fablabwinti/RFID_Machine_Controller/Firmware/Fablab_RFID_control/display.h

#include <Fonts/FreeSansBold12pt7b.h>


// "Fonts/g9regular.h" already included in global.h
#include "Fonts/g12bold.h"



#if (SSD1306_LCDHEIGHT != 64)
#error("Display height not set to 64 pixels, please fix Adafruit_SSD1306.h!");
#endif

#define POSTLOGOUTDISPLAYTIME 10 //time in seconds user info is displayed after logout


//logo generated using http://javl.github.io/image2cpp/
//note on icon generation: the library can only display bitmaps with the x dimension being a multiple of 8 so all icons must be in this format, other dimension screw up the displayed image
//the default settings on the webpage are fine (horizontal mode)

unsigned char fablablogo []  = {
  0x00, 0x00, 0x00, 0x00, 0x00, 0x00, 0x00, 0x00, 0x00, 0x00, 0x00, 0x7f, 0xf8, 0x00, 0x00, 0x00,
  0x00, 0x00, 0x07, 0xff, 0xff, 0x80, 0x00, 0x00, 0x00, 0x00, 0x1f, 0xff, 0xff, 0xf0, 0x00, 0x00,
  0x00, 0x00, 0x7f, 0x80, 0x07, 0xfc, 0x00, 0x00, 0x00, 0x01, 0xf8, 0x00, 0x00, 0x3f, 0x00, 0x00,
  0x00, 0x07, 0xe0, 0x00, 0x00, 0x1f, 0x80, 0x00, 0x00, 0x0f, 0x80, 0x00, 0x00, 0x07, 0xc0, 0x00,
  0x00, 0x1e, 0x00, 0x7f, 0xf8, 0x03, 0xe0, 0x00, 0x00, 0x3c, 0x03, 0xff, 0xff, 0x00, 0xf0, 0x00,
  0x00, 0x78, 0x0f, 0xfc, 0xff, 0xc0, 0x78, 0x00, 0x00, 0xf0, 0x3f, 0xf0, 0x7f, 0xf0, 0x3c, 0x00,
  0x01, 0xe0, 0xff, 0xe0, 0x1f, 0xf8, 0x1e, 0x00, 0x03, 0xc1, 0xff, 0x80, 0x07, 0xfe, 0x0f, 0x00,
  0x07, 0x83, 0xff, 0xe0, 0x01, 0xff, 0x07, 0x00, 0x07, 0x07, 0xff, 0xff, 0xe0, 0xff, 0x87, 0x80,
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
  0x3E, 0x00, 0x00, 0x7C, 0x1C, 0x00, 0x00, 0x38
};

//print the header: machine name and status icons
void displayAddHeader(void) {

  display.setFont(&g9regularFont);
  display.setCursor(0, 7);


  display.print(config.MachineName);

  if (WiFi.status() == WL_CONNECTED)
  {

    display.drawBitmap(94, 0, wifiokicon, 9, 7, 1);
  }
  else
  {
    display.drawBitmap(94, 0, wififailicon, 9, 7, 1);
  }
  if (userDBupdated)
  {
    display.drawBitmap(105, 0, DBokicon, 6, 7, 1);
  }
  else
  {
    display.drawBitmap(105, 0, DBfailicon, 6, 7, 1);
  }
  if (serverhealthy)
  {
    display.drawBitmap(113, 0, serverokicon, 7, 7, 1);
  }
  else
  {
    display.drawBitmap(113, 0, serverfailicon, 7, 7, 1);

  }

  if (SDcardOK)
  {
    display.drawBitmap(122, 0, SDokicon, 8, 7, 1);
  }
  else
  {
    display.drawBitmap(122, 0, SDfailicon, 8, 7, 1);
  }

  display.drawFastHLine(0, 8, 128, 1); //draw horizontal line
}

//display user info during login or post logout
void displayUserInfo(void)
{
  String fullname;
  //String firstname;
  //String surname;
  if (currentuser == 0) //the admin tag is logged in
  {
    fullname = "MASTER KEY";
  }
  else
  {
    //get current users name from database
    userdatabase.readRec(currentuser, EDB_REC userentry); //get the currently logged in user entry
    fullname = String(userentry.name);
    //firstname = splitStringbySeparator(fullname, char(' ')); //split the name string into first name and surname
    //surname = fullname.substring(firstname.length() + 1);
  }

  if (machineLocked)
  {
    fullname = " "; //currentuser is 0 after logout, so name is no longer available (TODO: could save the 'lastuser' number in a global variable or something)
  }

  display.setFont(&g12boldFont);
  display.setCursor(0, 21);
  display.print(fullname);//String(userentry.name));

  //display.print(0, 27);
  //display.print(surname);
  display.setFont(&FreeSansBold12pt7b);

  time_t timeinuse;
  if (machineLocked) //if no user is logged in, this is a post logout call, display static time of time used
  {
    timeinuse = userStoptime - userStarttime;
  }
  else
    timeinuse = getRtcTimestamp() - userStarttime;

  uint16_t usehours = timeinuse / 3600;
  uint16_t useminutes = (timeinuse % 3600) / 60;
  uint16_t useseconds = timeinuse % 60;

  char temparr[12];
  // getTextBounds considers the bitmap size, not the advance width, so the
  // text width differs for a narrow glyph like '1' at the end, which makes
  // the text jump around. To avoid that, append a dummy char of known width
  // for measuring and remove it for rendering.
  snprintf(temparr, sizeof(temparr), "%u:%02u:%02u.", usehours, useminutes, useseconds);
  int16_t x, y;
  uint16_t w1, w2, h;
  display.getTextBounds(temparr, 0, 0, &x, &y, &w1, &h);
  temparr[strlen(temparr) - 1] = '\0';
  w1 -= 5;
  display.setCursor(64 - w1 / 2, 46);
  display.print(temparr);


  //running cost is calculated from:
  // config.mPrice //price per period in cents
  // config.mPeriod //pricing period in minutes
  //config.mMinPeriods /minimum periods that are billed
  //to not bill accidental login, the first 30 seconds are free

  uint16_t cost = 0; //cost in cents
  if(timeinuse > 30) //after 30 seconds, start counting cost, bill the minimum amount, then increase by pricing period
  {
    //initially, bill the minimum number of periods
    cost = config.mMinPPrice;
    //after minimum number of periods, start counting periods
    if(timeinuse > 60*(time_t)config.mMinPeriods*(time_t)config.mPeriod) 
    {
      time_t periodSeconds = 60*(time_t)config.mPeriod;
      uint16_t numberofperiods = (timeinuse + periodSeconds - 1)/periodSeconds; // rounded up
      cost += (numberofperiods - config.mMinPeriods)*config.mPrice;
    }
  }
  
  snprintf(temparr, sizeof(temparr), "%d.%02d.", cost / 100, cost % 100);
  display.setFont(&g12boldFont);
  display.getTextBounds(temparr, 0, 0, &x, &y, &w1, &h);
  temparr[strlen(temparr) - 1] = '\0';
  w1 -= 3;
  display.setCursor(128 - w1, 63);
  display.print(temparr);
  display.setFont(&g9regularFont);
  display.getTextBounds("CHF", 0, 0, &x, &y, &w2, &h);
  display.setCursor(128 - w1 - w2 - 5, 63);
  display.print("CHF");

}

void displayUpdate(void) {


  //stuff to display: time
  //currently logged in user

  //if machine is unused:
  //display the current time, maybe also the date, what else?
  display.clearDisplay();
  displayAddHeader();


  if (machineLocked) //machine not in use
  {
    if ( postlogoutmillis > 0 && millis() < postlogoutmillis + (long)POSTLOGOUTDISPLAYTIME * 1000) //user just logged out, postlogoutmillis is set to 0 after postlogout switchoff (of after 30 seconds, whichever one is longer)
    {
      displayUserInfo();
    }
    else //idle
    {
      char temparr[11];
      snprintf(temparr, sizeof(temparr), "%02u.%02u.%04u", day(), month(), year());
      display.setFont(&g9regularFont);
      display.setCursor(37, 33);
      display.print(temparr);
      snprintf(temparr, sizeof(temparr), "%02u:%02u:%02u", hour(), minute(), second());
      display.setFont(&g12boldFont);
      display.setCursor(35, 47);
      display.print(temparr);

      //todo: remove this debug IP output (or if it is deemed useful in production, properly integrate it into the layout)

      if (WiFi.status() == WL_CONNECTED)
      {
        display.setFont(&g9regularFont);
        display.setCursor(0, 63);
        display.print(F("IP: "));
        display.print(WiFi.localIP());
      }
    }
  }
  else //machine is unlocked, user is logged in
  {
    displayUserInfo();
  }

  display.display();

  // char numberbuffer[6];
  //dtostrf(1234, 6, 2, numberbuffer);
  //display.print(numberbuffer);

}


void displayLogin(void)
{
  display.clearDisplay();
  displayAddHeader();

  //todo: display username of recognized tag
#if 0
  display.setFont(&g12boldFont);
  display.setCursor(0, 21);
  display.print("Master");
#endif
  display.setFont(&FreeSansBold12pt7b);
  display.setCursor(44, 51);

  // display.drawBitmap(3, 30, accepticon, 24, 24, 1);
  //display.setFont(&Dialogbold20);
  // display.setCursor(38, 48);

  display.print("Start   ");
  display.drawXBitmap(5, 27, check_xbm_bits, check_xbm_width, check_xbm_height, 1);
  display.display();
}

void displayLogout(void)
{
  display.clearDisplay();
  displayAddHeader();

  //todo: display username of recognized tag
#if 0
  display.setFont(&g12boldFont);
  display.setCursor(0, 21);
  display.print("name");
#endif
  display.setFont(&FreeSansBold12pt7b);
  display.setCursor(44, 51);

  // display.drawBitmap(3, 30, accepticon, 24, 24, 1);
  // display.setFont(&Dialogbold20);
  // display.setCursor(38, 48);

  display.print("Stop     ");
  display.drawXBitmap(5, 27, check_xbm_bits, check_xbm_width, check_xbm_height, 1);
  display.display();
}

//display access denied (with a reason)
//reasons: 0 = unauthorized, 1 = occupied, 2 = invalid tag
void displayDenied(uint8_t reason)
{
  display.clearDisplay();
  displayAddHeader();

  display.setFont(&g12boldFont);
  //todo: display username of recognized tag (if any)
#if 0
  display.setFont(&g12boldFont);
  display.setCursor(0, 21);
  display.print("name");
#endif
  display.setCursor(44, 46);

  // display.drawBitmap(0, 30, deniedicon, 24, 24, 1);
  // display.setFont(&Dialogbold12);
  // display.setCursor(25, 46);

  if (reason == 1)
  {
    display.print("besetzt");
  }
  else if (reason == 2)
  {
    display.print("tag error");
  }
  else
  {
    display.print("unberechtigt");
  }
  display.drawXBitmap(5, 27, cross_xbm_bits, cross_xbm_width, cross_xbm_height, 1);
  display.display();
}


void showCloudDownload(void)
{
  display.clearDisplay();
  display.drawBitmap(46, 20, DBdl, 32, 32, 1);
  display.setFont(&g12boldFont);
  display.setCursor(12, 12);
  display.println(F("Updating Database"));
  display.display();
}

void displayinit(void)
{
  display.begin(SSD1306_SWITCHCAPVCC, 0x3C);
  Wire.setClock(400000);  // use fast speed
  display.clearDisplay();
  display.display();  //
  display.setTextSize(1);
  display.setTextColor(WHITE);
  display.setTextWrap(false);

  /*
    display.setCursor(29, 15);
    display.setFont(&FreeSansBold12pt7b);
    display.println("Fablab");
    display.setCursor(30, 54);
    display.print("Winti");
    display.display();
  */
  //delay(500);
  display.drawBitmap(31, 0, fablablogo, 64, 64, 1);
  display.display();
  delay(800);
  display.clearDisplay();
  display.display();

  display.setFont(&g9regularFont);
  display.setCursor(0, 7);


}
