fablabwinti/RFID_Machine_Controller/Firmware/Fablab_RFID_control/WiFi.h

//#include <DNSServer.h>

#define APTIMEOUT (10*60000) //stop accesspoint mode after this time
#define DNS_PORT 53

ESP8266WiFiMulti wifiMulti;
uint8_t wifiConnected;
uint8_t wifiConnectFailCounter;
unsigned long wifiwatchdog = 0; //time keeper for wifi connection
unsigned long APtimestamp = 0; //time keeper for wifi connection
//DNSServer dnsServer;

/*
  void setupMDNS()
  {
  // Call MDNS.begin(<domain>) to set up mDNS to point to
  // "<domain>.local" or in this case alphanode.local
  if (!MDNS.begin("rfidcontrol"))
  {
    Serial.println(F("Error setting up MDNS responder!"));
  }
  else  Serial.println(F("mDNS responder started"));
  }
*/


//host a wifi access point
void wifiHostAP()
{
  //IPAddress apIP(192, 168, 4, 1);
  WiFi.disconnect(true);
  delay(100);
#ifdef SERIALDEBUG
  Serial.print(F("Starting access point. "));
#endif
  WiFi.mode(WIFI_AP); //accesspoint is very unstable if STA mode is on and no wifi connection is available
  WiFi.softAP(config.DeviceName.c_str(), config.DevicePW.c_str());
  //dnsServer.setErrorReplyCode(DNSReplyCode::NoError);
  //dnsServer.start(DNS_PORT, "*", apIP);

  APactive = 2; //AP is up and running
  APtimestamp = millis();
  LEDColor.h = 200; //set LED purple if accesspoint is active
  LEDColor.v = LED_MAXBRIGHTNESS; //high brightness

}

//add accesspoints saved in config to wifiMulti
void wifiConnect(void)
{
  wifiConnected = 0; //if this function is called, we are not yet or no more connected
  uint8_t i;
#ifdef SERIALDEBUG
  Serial.println(F("Connecting to WIFI"));
#endif
  //add all known connections in config to wifi multi:
  for (i = 0; i < MULTIWIFIS ; i++)
  {
    wifiMulti.addAP(config.ssid[i].c_str(), config.wifipass[i].c_str());
#ifdef SERIALDEBUG
    Serial.print(F("Adding Network: "));
    Serial.println(config.ssid[i]);
#endif
  }

  wifiMulti.run(); //connect to wifi (starts the network scan on first call, tries to connect on further calls (in checkconnection function)
}


void wifiAddAP(String name, String password)
{
  uint8_t success = 1;
  uint8_t i;
#ifdef SERIALDEBUG
  Serial.println(name + " " + password);
#endif
  for (i = 0; i < MULTIWIFIS ; i++)
  {
    if (config.ssid[i] == name) //already known,maybe an updated password?
    {

      if (config.wifipass[i] != password) //updated password
      {
        config.wifipass[i] = password;
      }
      else
      {
        success = 0;
      }
    }
  }

  if (success)
  {
    config.ssid[config.nextmultiwifitowrite] = name;
    config.wifipass[config.nextmultiwifitowrite] = password;
    config.nextmultiwifitowrite = (config.nextmultiwifitowrite + 1) % MULTIWIFIS;
    WriteConfig();
#ifdef SERIALDEBUG
    Serial.println(F("wifi saved"));
#endif
  }
}


void wifiCheckConnection()
{

  //todo: set a timeout for connecting to wifi, if connection fails repeatedly, start the AP

  if (APactive > 0)
  {
    if (((millis() - APtimestamp) > APTIMEOUT) )
    {
      WiFi.mode(WIFI_STA); //deactivate access point
      APactive = 0;
      LEDColor.h = 30; //change led color to yellow
      LEDColor.v = LED_DEFAULTBRIGTHNESS;
      ESP.restart(); //todo: this was added because the mdns service does not work after returning from AP mode, can this be fixed some other way?
    }

    if (APactive == 1) wifiHostAP(); //AP was requested, so run it
    else if (APactive == 2)
    {
      LEDColor.h = 200; //keep LED purple if accesspoint is active
      LEDColor.v = LED_MAXBRIGHTNESS; //high brightness
    }
    return; //do not handle normal wifi connection in AP mode
  }

  if (WiFi.status() == WL_CONNECTED)
  {
    wifiConnectFailCounter = 0;
    if (wifiConnected == 0) //if we were not connected before, setup services
    {
      wifiConnected = 1;
      LED_blink_once(170); //blink in blue upon connection
      timeManager(true); //force an NTP time update

      String logstring = getTimeString();
      logstring += "\tConnected to WIFI";
#ifdef SERIALDEBUG
      Serial.print(logstring);
      Serial.print(" IP = ");
      Serial.println(WiFi.localIP());
#endif
      SDwriteLogfile(logstring);

    }

  }
  else if (APactive == 0) {
    wifiConnected = 0;

    //try to reconnect every 2 seconds if AP is not active
    if (millis() - wifiwatchdog > 2000)
    {
      LED_blink_once(10); //blink in orange when not connected
      wifiConnectFailCounter++;
#ifdef SERIALDEBUG
      Serial.println(F("(re)connecting wifi"));
#endif
      wifiwatchdog = millis();
      switch (wifiMulti.run()) {
        case WL_CONNECTED:
          if (!config.useDHCP)
          {
            WiFi.config(config.IP, config.Gateway , config.Netmask);
          }
#ifdef SERIALDEBUG
          Serial.println(F("Connected to:"));
          Serial.print(F("SSID: "));
          Serial.println(WiFi.SSID().c_str());
          Serial.print("IP: ");
          Serial.println(WiFi.localIP());
#endif
          break;
        case WL_NO_SSID_AVAIL:
#ifdef SERIALDEBUG
          Serial.println(F("Connecting Failed AP not found"));
#endif
          break;
        default:
#ifdef SERIALDEBUG
          Serial.println(F("WiFi Connect Failed."));
#endif
          break;
      }
    }
  }
}


void ConfigureWifi()
{
  display.println(F("Starting WiFi"));
  display.display();

  WiFi.persistent(false); //do not write SSID and password on every wifi connect, prevents flash wearout
  wifiConnectFailCounter = 0;
  //WiFi.disconnect(true); //delete any old wifi configuration (not needed with wifi multi)
  wifiwatchdog = millis();
  WiFi.mode(WIFI_STA); //set STA mode
  //WiFi.setSleepMode(WIFI_LIGHT_SLEEP); //enable light sleep mode to save power
  //wifi_fpm_set_sleep_type(LIGHT_SLEEP_T);
  wifiConnect(); //connect to wifi

}

//disconnect and disable wifi during machine running times to not be disturbed
void disableWifi()
{
#ifdef SERIALDEBUG
  Serial.print(F("disabling wifi."));
#endif
  WiFi.disconnect();
  delay(200);

  ESP.wdtFeed();

  // WiFi.mode(WIFI_OFF); //turning wifi off can cause crashes... must be a core bug so keep it running and just disconnect
  // WiFi.forceSleepBegin(100); //force sleep begin
  // delay(100);
#ifdef SERIALDEBUG
  Serial.println(F("disabled"));
#endif
}

//re-enable wifi, call this function after 'disableWifi()'
void enableWifi()
{
  // WiFi.forceSleepWake();
  ConfigureWifi();
}
